MatteoSpadetto/clock_alarm/Clock/include/imu.h

//                             ___          ___                 ___          ___         ___     //
//                            /\__\        /\  \               /\__\        /\__\      /|  |     //
//                 ___       /:/ _/_       \:\  \       ___   /:/ _/_      /:/ _/_    |:|  |     //
//                /\__\     /:/ /\  \       \:\  \     /\__\ /:/ /\  \    /:/ /\__\   |:|  |     //
//  ___     ___  /:/__/    /:/ /::\  \  ___ /::\  \   /:/  //:/ /::\  \  /:/ /:/  / __|:|__|     //
// /\  \   /\__\/::\  \   /:/__\/\:\__\/\  /:/\:\__\ /:/__//:/_/:/\:\__\/:/_/:/  / /::::\__\_____//
// \:\  \ /:/  /\/\:\  \__\:\  \ /:/  /\:\/:/  \/__//::\  \\:\/:/ /:/  /\:\/:/  /  ~~~~\::::/___///
//  \:\  /:/  /  ~~\:\/\__\\:\  /:/  /  \::/__/    /:/\:\  \\::/ /:/  /  \::/__/       |:|~~|    //
//   \:\/:/  /      \::/  / \:\/:/  /    \:\  \    \/__\:\  \\/_/:/  /    \:\  \       |:|  |    //
//    \::/  /       /:/  /   \::/  /      \:\__\        \:\__\ /:/  /      \:\__\      |:|__|    //
//     \/__/        \/__/     \/__/        \/__/         \/__/ \/__/        \/__/      |/__/     //

#ifndef _IMU_H
#define _IMU_H

#include <Arduino.h>

#define IMU_LIM1 4000 //Acceleration limit to cause a RGB color change
#define IMU_LIM2 6000 //Acceleration limit to cause a RGB color change

#define MAX_COLOR 255 //Max brigthness that it's possible to require in ordere to not need too much current
#define MIN_COLOR 30

const int MPU_addr = 0x68;                 //I2C address of the MPU-6050
int16_t AcX, AcY, AcZ, Tmp, GyX, GyY, GyZ; //IMU values

int mode;
int timeWaitTot;
int timeWait;

void IMUI2CInit(); //Initializing I2C form IMU
void readIMU();    //Reading from IMU
void imuRGB();     //Controlling leds with IMU
void imuStopAlarm();
void imuColorSet();

#endif
